tebl/VU-Switch/gallery/2021-04-09 02.41.15.jpg

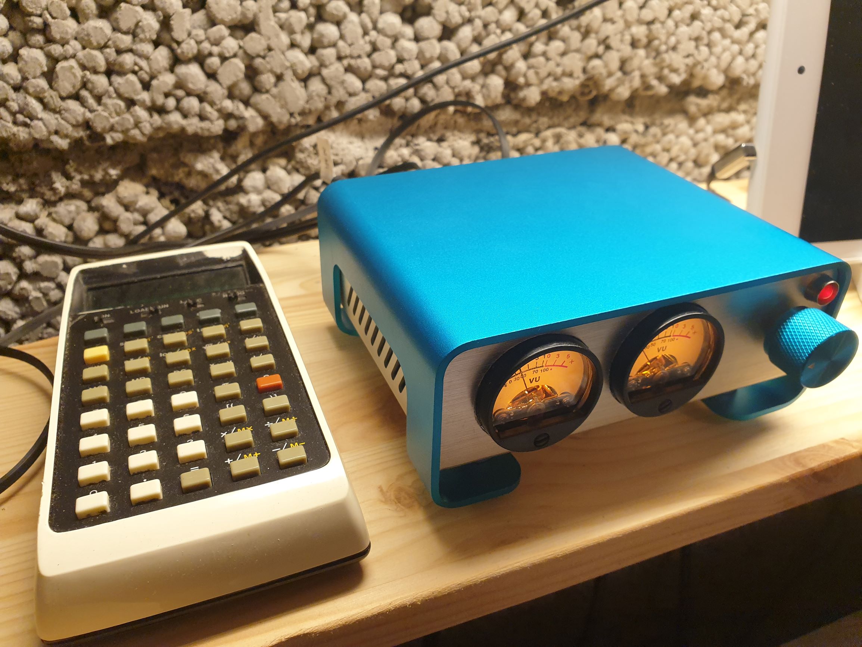
gallery/2021-04-09 02.41.15.jpg
